LuiCat/IIDX-Katboard/arduino/iidx_leo/Joystick.cpp

/*
  Joystick.cpp

  Copyright (c) 2015, Matthew Heironimus

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
  You should have received a copy of the GNU Lesser General Public
  License along with this library; if not, write to the Free Software
  Foundation, Inc., 51 Franklin St, Fifth Floor, Boston, MA  02110-1301  USA
*/

#include "Joystick.h"

#if defined(_USING_HID)

#define JOYSTICK_REPORT_ID 0x03

static const uint8_t _hidReportDescriptor[] PROGMEM = {
  
	// Joystick
	0x05, 0x01,			      // USAGE_PAGE (Generic Desktop)
	0x09, 0x04,			      // USAGE (Joystick)
	0xa1, 0x01,			      // COLLECTION (Application)
	0x85, JOYSTICK_REPORT_ID, //   REPORT_ID (3)

	// 12 Buttons
	0x05, 0x09,			      //   USAGE_PAGE (Button)
	0x19, 0x01,			      //   USAGE_MINIMUM (Button 1)
	0x29, 0x0C,			      //   USAGE_MAXIMUM (Button 12)
	0x15, 0x00,			      //   LOGICAL_MINIMUM (0)
	0x25, 0x01,			      //   LOGICAL_MAXIMUM (1)
	0x75, 0x01,			      //   REPORT_SIZE (1)
	0x95, 0x0C,			      //   REPORT_COUNT (12)
	0x55, 0x00,			      //   UNIT_EXPONENT (0)
	0x65, 0x00,			      //   UNIT (None)
	0x81, 0x02,			      //   INPUT (Data,Var,Abs)
 
  // 4 bit Padding
  0x95, 0x01,           //   REPORT_COUNT (1)
  0x75, 0x04,           //   REPORT_SIZE (4)
  0x81, 0x01,           //   INPUT (Constant)

	// X Axis
  0x05, 0x01,                    /*     USAGE_PAGE (Generic Desktop) */ 
  0x09, 0x30,                    /*     USAGE (X) */ 
  0x15, 0x00,                    /*     LOGICAL_MINIMUM (0) */ 
  0x26, 0xFF, 0x00,              /*     LOGICAL_MAXIMUM (255) */ 
  0x95, 0x01,                    /*     REPORT_COUNT (1) */ 
  0x75, 0x08,                    /*     REPORT_SIZE (08) */ 
  0x81, 0x02,                    /*     INPUT (Data,Var,Abs) */ 
                              
	0xC0				      // END_COLLECTION
};

Joystick_::Joystick_()
{
	// Setup HID report structure
	static HIDSubDescriptor node(_hidReportDescriptor, sizeof(_hidReportDescriptor));
	HID().AppendDescriptor(&node);
}

void Joystick_::sendState()
{
	HID().SendReport(JOYSTICK_REPORT_ID, this, sizeof(Joystick_));
}

Joystick_ Joystick;

#endif
